Unidad-Robotica-Dlab/Registro-PH/Software/data/prueba1_1s_22-03-2024 (copia).png

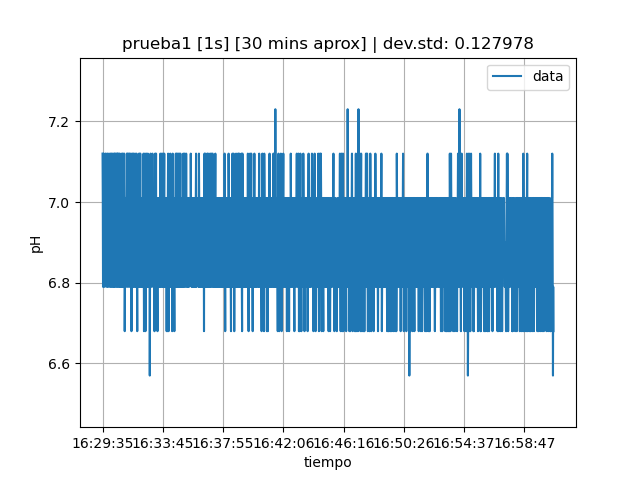
Software/data/prueba1_1s_22-03-2024 (copia).png
